harbra/ThermoLight/pcb/AP2112.sch

## KiCad design pcb/AP2112.sch (2019-01-05)

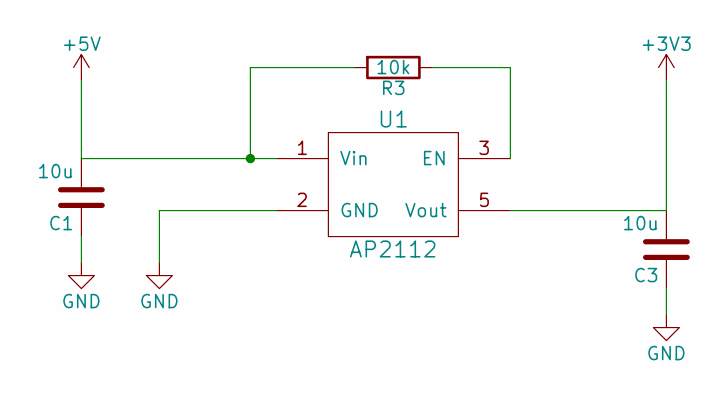
[picture p6: schematic AP2112.sch]

Parts:
C1, C3: 10u; C_1206_HandSoldering
R3: 10k; R_0603_HandSoldering
U1: AP2112; SOT-23-5_HandSoldering

Connections:
+3V3: C3.2, U1.5 (Vout)
+5V: C1.2, R3.2, U1.1 (Vin)
GND: C1.1, C3.1, U1.2 (GND)
unnamed: R3.1, U1.3 (EN)
