harbra/ThermoLight/pcb/esp-12s.sch

## KiCad design pcb/esp-12s.sch (2019-01-05)

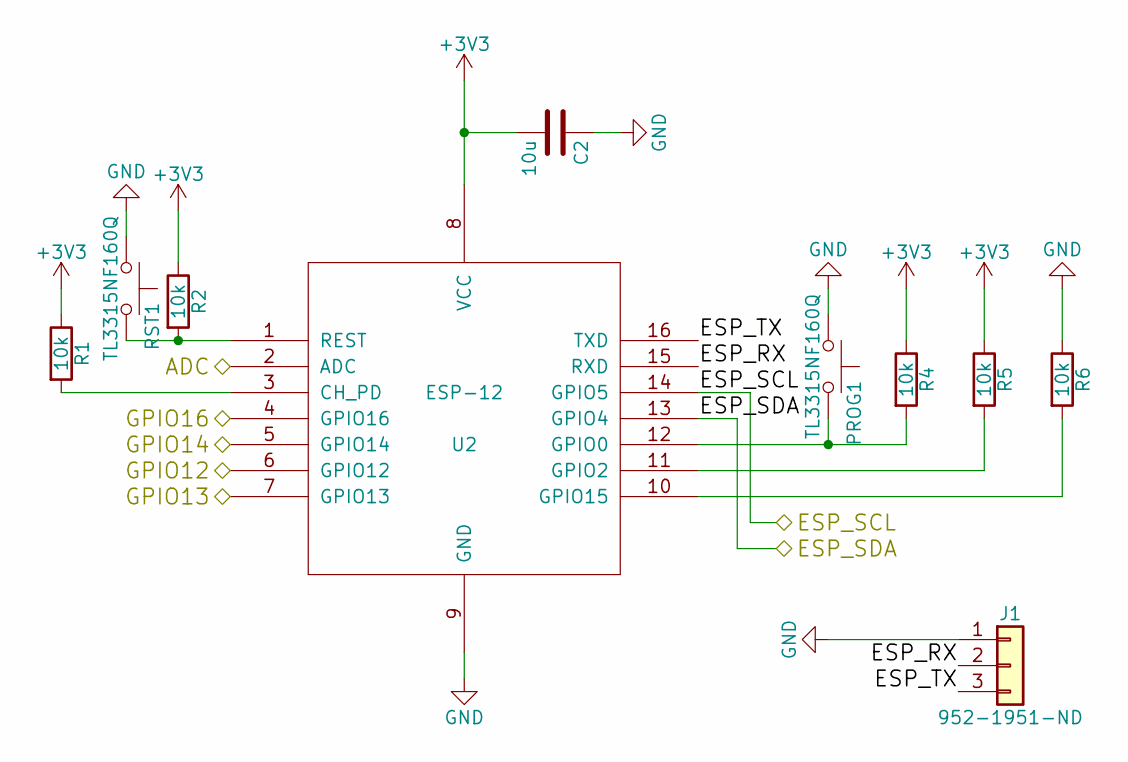
[picture p7: schematic esp-12s.sch]

Parts:
C2: 10u; C_1206_HandSoldering
J1: 952-1951-ND; Pin_Header_Straight_1x03_Pitch2.54mm_SMD_Pin1Right
PROG1: TL3315NF160Q; TL3315
R1, R2, R4, R5, R6: 10k; R_0603_HandSoldering
RST1: TL3315NF160Q; TL3315
U2: ESP-12; ESP-12S_SMD

Connections:
+3V3: C2.2, R1.1, R2.1, R4.1, R5.1, U2.8 (VCC)
ADC: U2.2 (ADC)
ESP_RX: J1.2, U2.15 (RXD)
ESP_SCL: U2.14 (GPIO5)
ESP_SDA: U2.13 (GPIO4)
ESP_TX: J1.3, U2.16 (TXD)
GND: C2.1, J1.1, PROG1.1, R6.1, RST1.1, U2.9 (GND)
GPIO12: U2.6 (GPIO12)
GPIO13: U2.7 (GPIO13)
GPIO14: U2.5 (GPIO14)
GPIO16: U2.4 (GPIO16)
unnamed: PROG1.2, R4.2, U2.12 (GPIO0)
unnamed: R1.2, U2.3 (CH_PD)
unnamed: R2.2, RST1.2, U2.1 (REST)
unnamed: R5.2, U2.11 (GPIO2)
unnamed: R6.2, U2.10 (GPIO15)
