harbra/ThermoLight/pcb/thermolight.sch

## KiCad design pcb/thermolight.sch (2019-01-05)

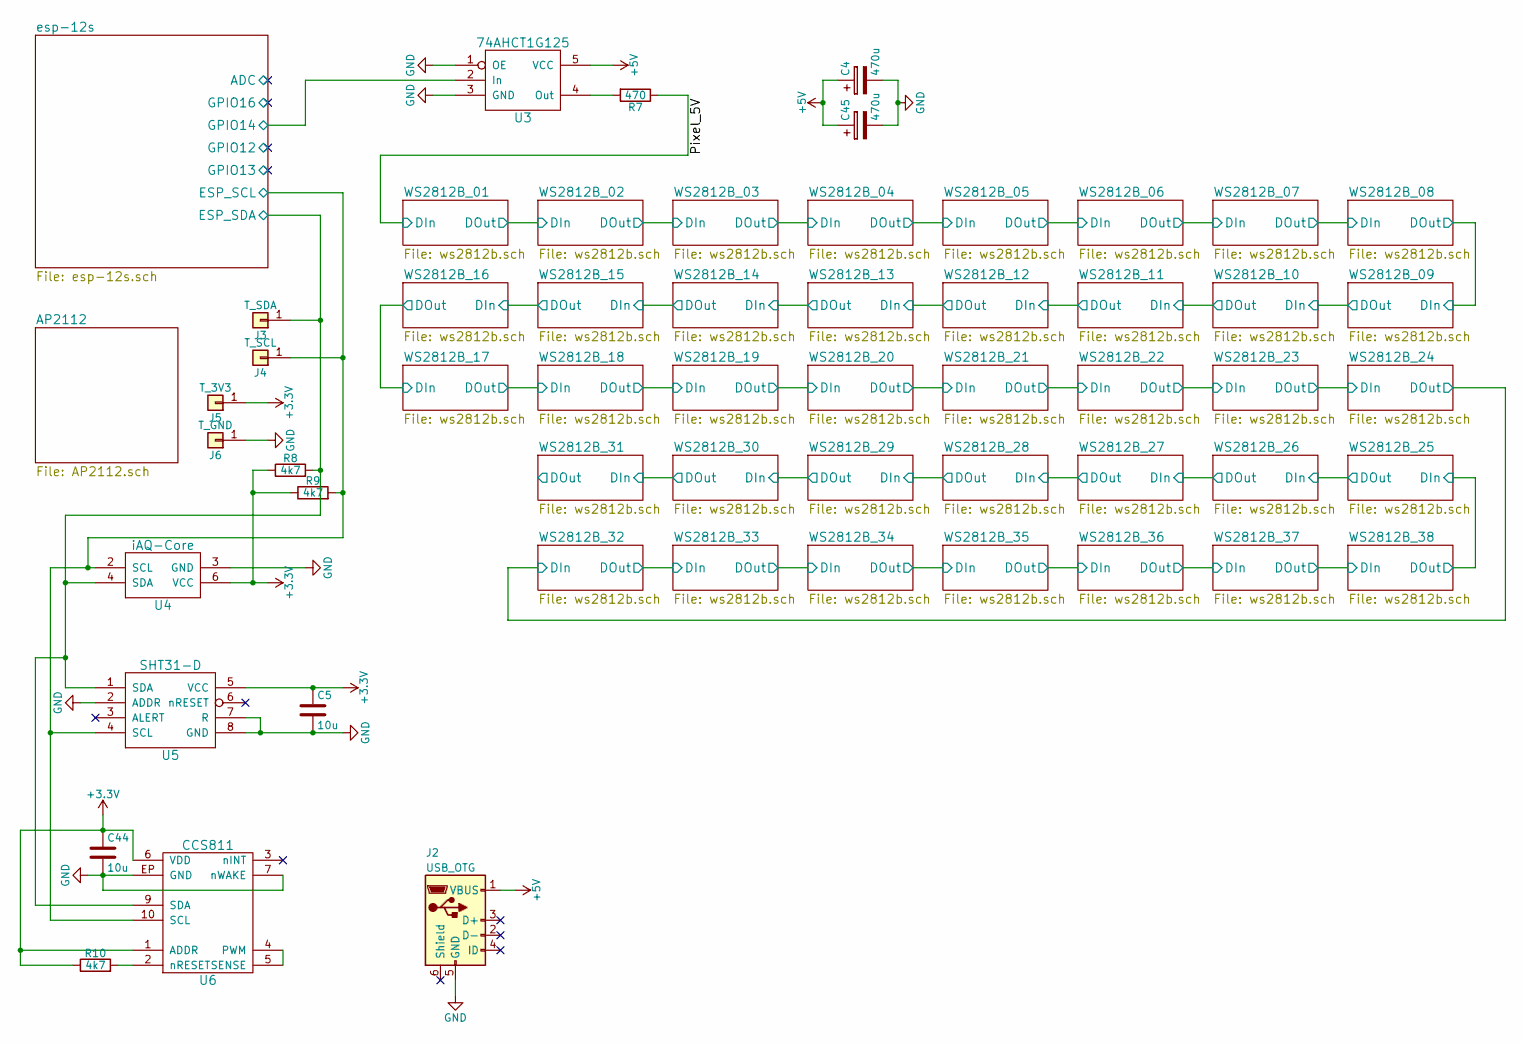
[picture p8: schematic thermolight.sch]

Parts:
C4, C45: 470u; CP_Radial_D6.3mm_P2.50mm_lying
C5, C44: 10u; C_1206_HandSoldering
J2: USB_OTG; 1051640001
J3: T_SDA; Pin_Header_Straight_1x01_Pitch2.54mm
J4: T_SCL; Pin_Header_Straight_1x01_Pitch2.54mm
J5: T_3V3; Pin_Header_Straight_1x01_Pitch2.54mm
J6: T_GND; Pin_Header_Straight_1x01_Pitch2.54mm
R7: 470; R_0603_HandSoldering
R8, R9, R10: 4k7; R_0603_HandSoldering
U3: 74AHCT1G125; SOT-23-5_HandSoldering
U4: iAQ-Core
U5: SHT31-D; DFN-8-2.5x2.5-0.5mm-handsolder
U6: CCS811; LGA_CCS811

Connections:
+3.3V: C5.1, C44.1, J5.1, R8.1, R9.1, R10.1, U4.6 (VCC), U5.5 (VCC), U6.1 (ADDR), U6.6 (VDD)
+5V: C4.1, C45.1, J2.1 (VBUS), U3.5 (VCC)
DIn: R7.1
ESP_SCL: J4.1, R9.2, U4.2 (SCL), U5.4 (SCL), U6.10 (SCL)
ESP_SDA: J3.1, R8.2, U4.4 (SDA), U5.1 (SDA), U6.9 (SDA)
GND: C4.2, C5.2, C44.2, C45.2, J2.5 (GND), J6.1, U3.1 (OE), U3.3 (GND), U4.3 (GND), U5.2 (ADDR), U5.7 (R), U5.8 (GND), U6.7 (nWAKE), U6.EP (GND)
GPIO14: U3.2 (In)
unnamed: R7.2, U3.4 (Out)
unnamed: R10.2, U6.2 (nRESET)
unnamed: U6.4 (PWM), U6.5 (SENSE)
