harbra/ThermoLight/pcb/ws2812b.sch

## KiCad design pcb/ws2812b.sch (2019-01-05)

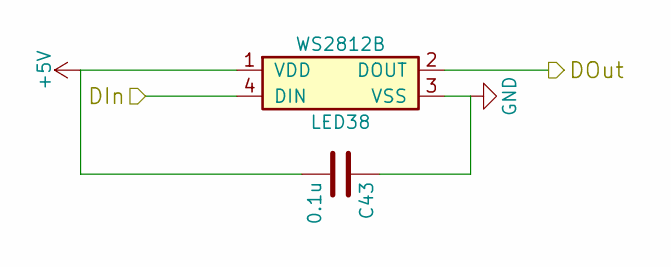
[picture p9: schematic ws2812b.sch]

Parts:
C6: 0.1u; C_0603_HandSoldering
LED1: WS2812B; LED_WS2812B-PLCC4

Connections:
+5V: C6.2, LED1.1 (VDD)
DIn: LED1.4 (DIN)
DOut: LED1.2 (DOUT)
GND: C6.1, LED1.3 (VSS)
